TMLKyza/MyHeavyNC/LCNC-config/qtvcp/screens/qtdragon/images/brushed_metal.png

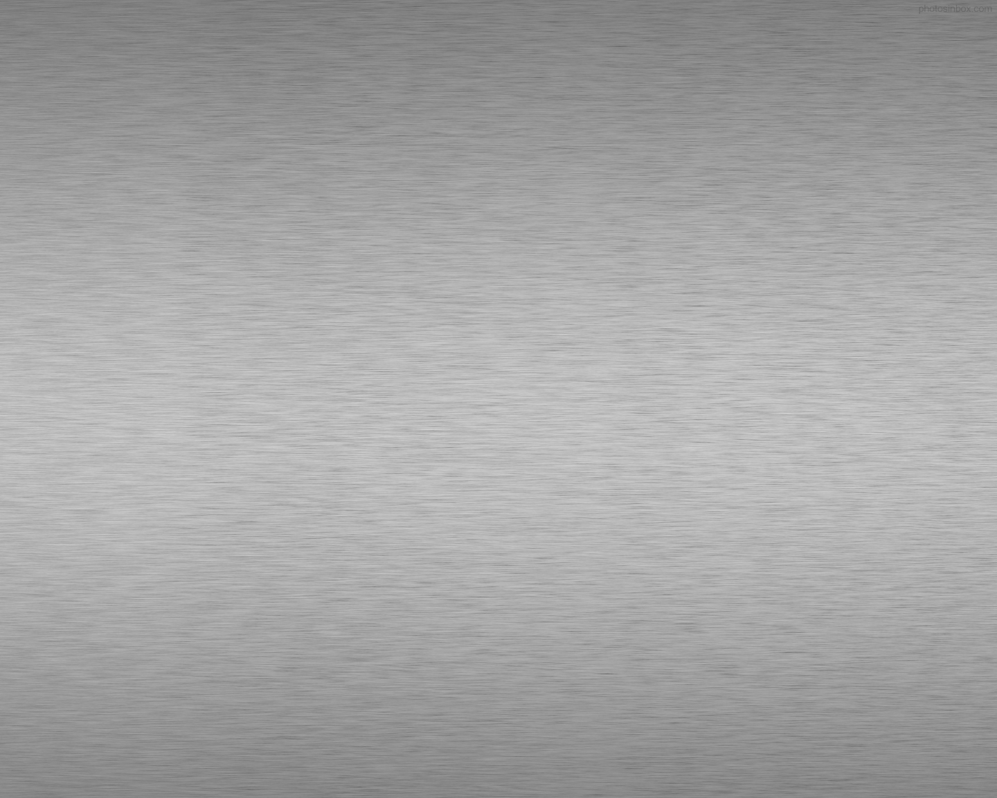
LCNC-config/qtvcp/screens/qtdragon/images/brushed_metal.png
