TMLKyza/MyHeavyNC/LCNC-config/qtvcp/screens/qtdragon/images/atc_spindle_tool.png

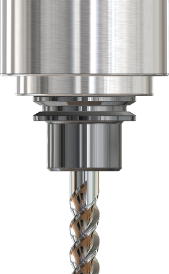
LCNC-config/qtvcp/screens/qtdragon/images/atc_spindle_tool.png
