TMLKyza/MyHeavyNC/LCNC-config/qtvcp/screens/qtdragon/images/Left_arrow.png

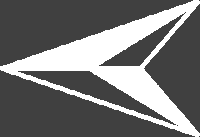
LCNC-config/qtvcp/screens/qtdragon/images/Left_arrow.png
