TMLKyza/MyHeavyNC/LCNC-config/qtvcp/screens/qtdragon/images/Right_arrow.png

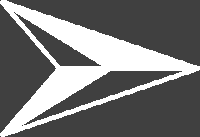
LCNC-config/qtvcp/screens/qtdragon/images/Right_arrow.png
