TMLKyza/MyHeavyNC/LCNC-config/qtvcp/screens/qtdragon/images/tool_probe.png

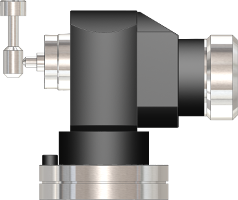
LCNC-config/qtvcp/screens/qtdragon/images/tool_probe.png
