TMLKyza/MyHeavyNC/LCNC-config/qtvcp/screens/qtdragon/images/x_minus_jog_button.png

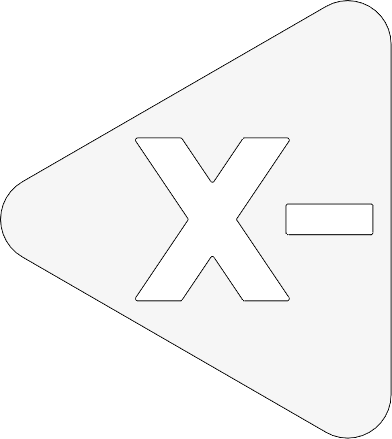
LCNC-config/qtvcp/screens/qtdragon/images/x_minus_jog_button.png
