TMLKyza/MyHeavyNC/LCNC-config/qtvcp/screens/qtdragon/images/x_plus_jog_button.png

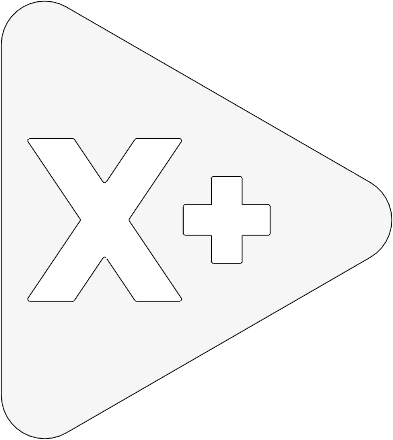
LCNC-config/qtvcp/screens/qtdragon/images/x_plus_jog_button.png
