TMLKyza/MyHeavyNC/LCNC-config/qtvcp/screens/qtdragon/images/y_plus_jog_button.png

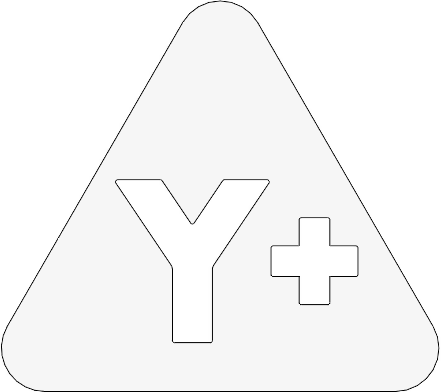
LCNC-config/qtvcp/screens/qtdragon/images/y_plus_jog_button.png
