TMLKyza/MyHeavyNC/LCNC-config/qtvcp/screens/qtdragon/images/z_minus_jog_button.png

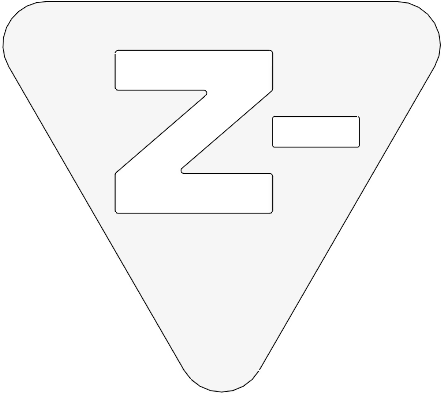
LCNC-config/qtvcp/screens/qtdragon/images/z_minus_jog_button.png
