TMLKyza/MyHeavyNC/CAD/Users/CAD/Documents/SOLIDWORKS/Router/parts/Yaxis/YstepperMount.step

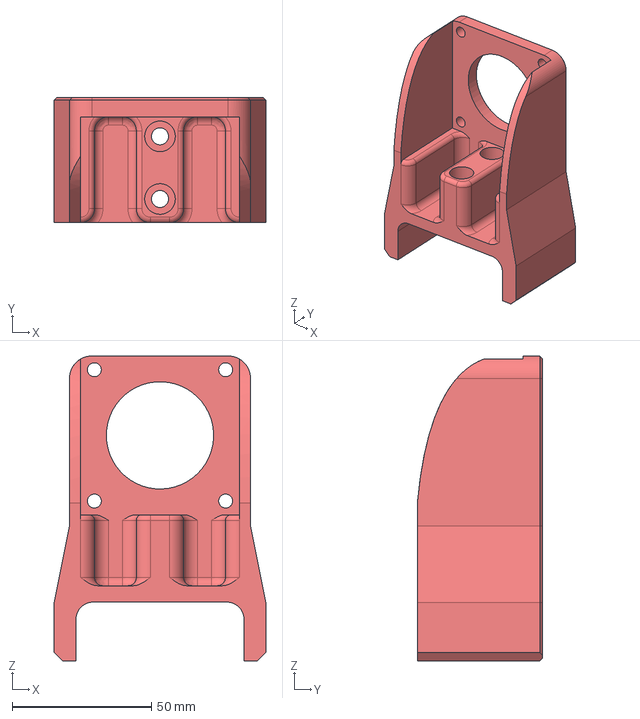
[picture p26: CAD file, 2024-07-04]
CAD/Users/CAD/Documents/SOLIDWORKS/Router/parts/Yaxis/YstepperMount.step
76.0 x 45.0 x 109.5 mm
