TMLKyza/MyHeavyNC/CAD/Users/CAD/Documents/SOLIDWORKS/Router/parts/Zaxis/motorSupport.SLDPRT

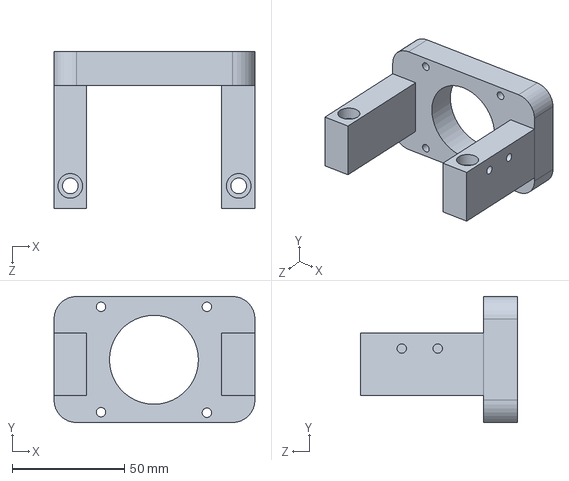
[picture p27: CAD file, 2024-07-04]
CAD/Users/CAD/Documents/SOLIDWORKS/Router/parts/Zaxis/motorSupport.SLDPRT
89.5 x 56.2 x 69.8 mm
