TMLKyza/MyHeavyNC/CAD/Users/CAD/Documents/SOLIDWORKS/vice/jaws.SLDPRT

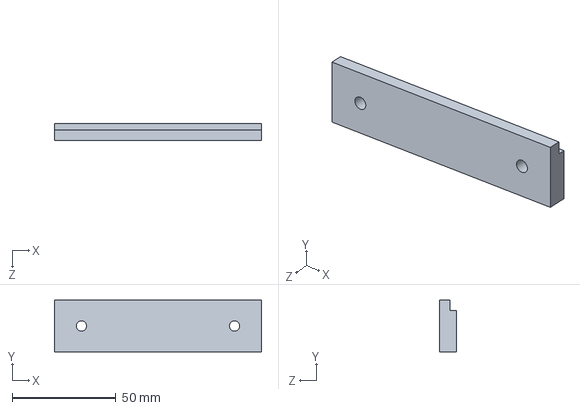
[picture p28: CAD file, 2024-07-04]
CAD/Users/CAD/Documents/SOLIDWORKS/vice/jaws.SLDPRT
100.0 x 25.0 x 8.00 mm
