TMLKyza/MyHeavyNC/CAD/parts/HRG25Rail.SLDPRT

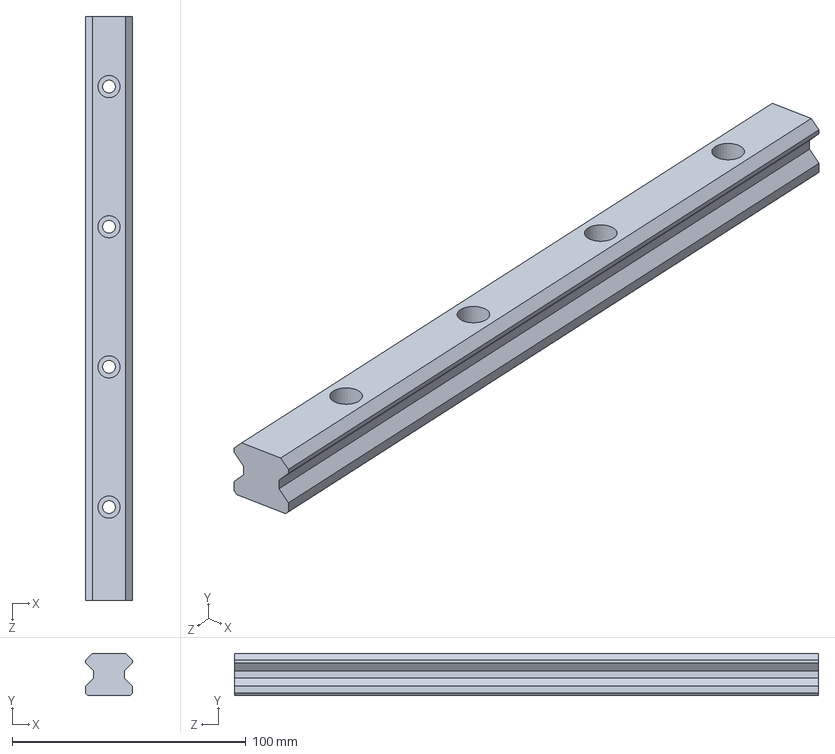
[picture p29: CAD file, 2024-07-04]
CAD/parts/HRG25Rail.SLDPRT
20.0 x 18.0 x 250.0 mm
