TMLKyza/MyHeavyNC/CAD/parts/Xaxis/support BF12.step

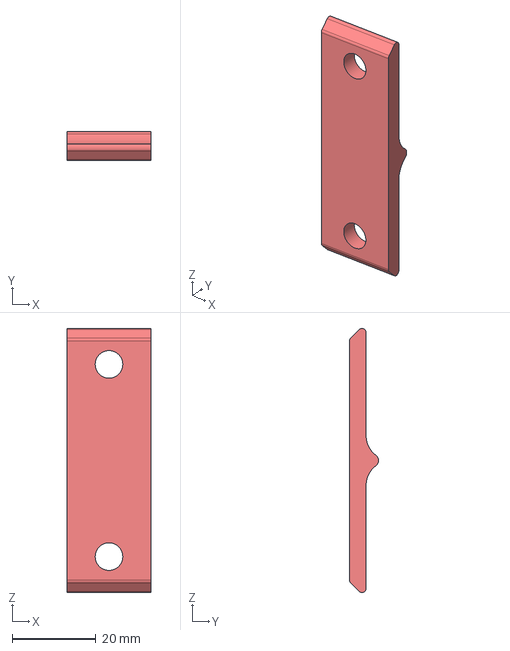
[picture p30: CAD file, 2024-07-04]
CAD/parts/Xaxis/support BF12.step
20.0 x 7.00 x 63.2 mm
