TMLKyza/MyHeavyNC/CAD/parts/Yaxis/Yaxis_tube.SLDPRT

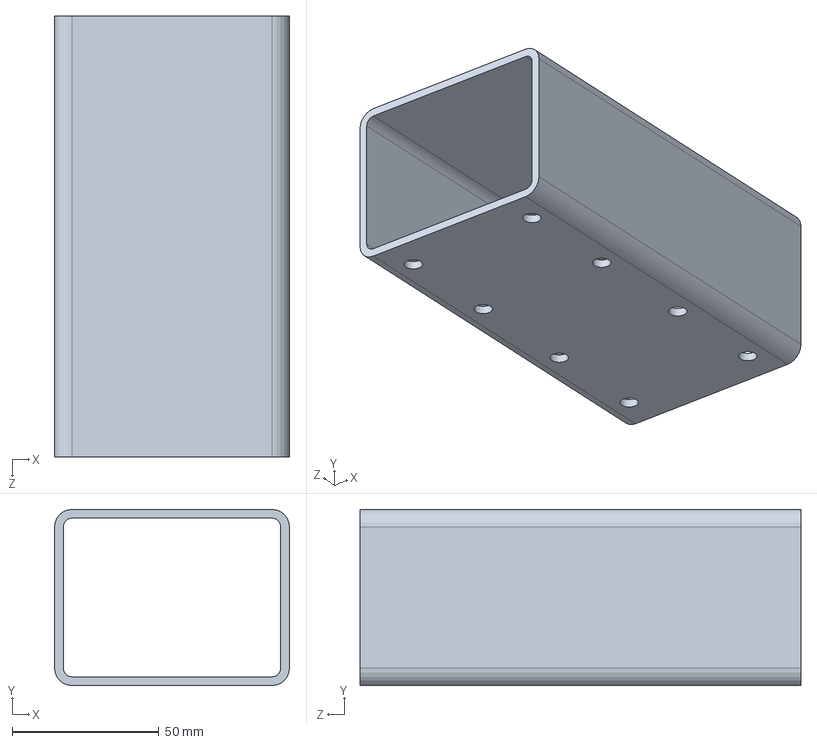
[picture p31: CAD file, 2024-07-04]
CAD/parts/Yaxis/Yaxis_tube.SLDPRT
80.0 x 60.0 x 150.0 mm
