TMLKyza/MyHeavyNC/CAD/Users/CAD/Documents/SOLIDWORKS/Router/parts/Xaxis/XsensorSupport.SLDPRT

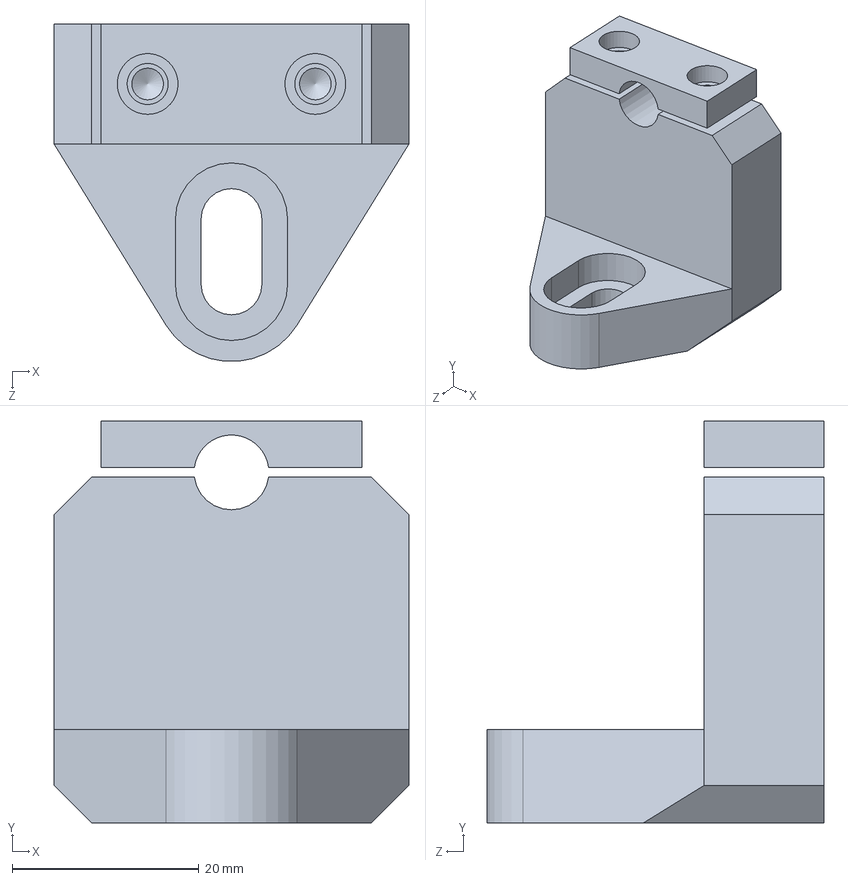
[picture p32: CAD file, 2024-07-04]
CAD/Users/CAD/Documents/SOLIDWORKS/Router/parts/Xaxis/XsensorSupport.SLDPRT
37.9 x 43.0 x 36.1 mm
