TMLKyza/MyHeavyNC/CAD/Users/CAD/Documents/SOLIDWORKS/Router/parts/Zaxis/SFU1204-nutCasing.SLDPRT

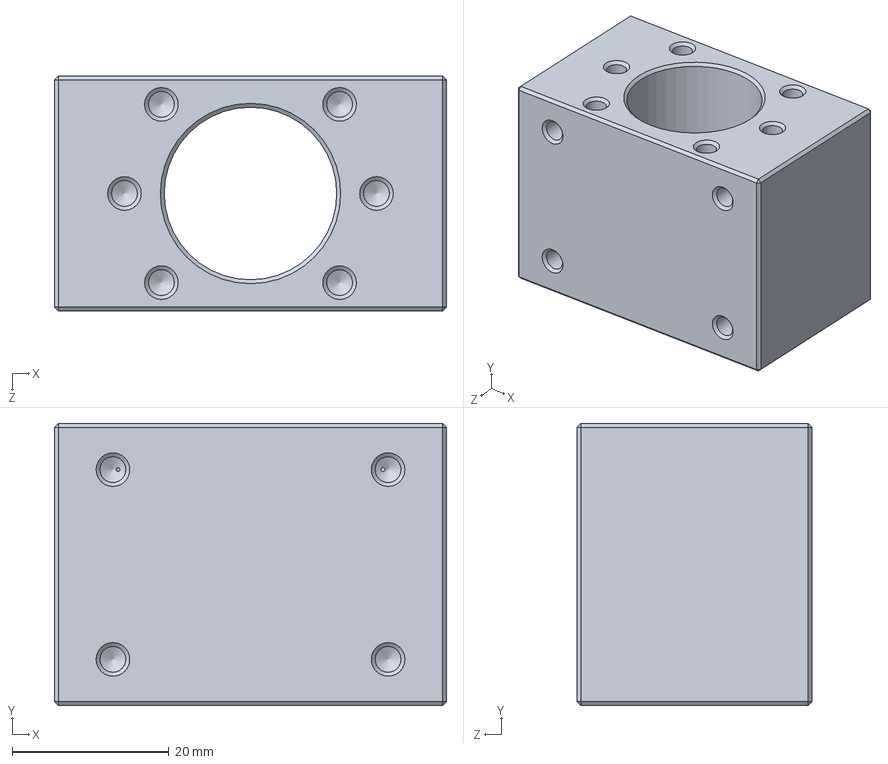
[picture p33: CAD file, 2024-07-04]
CAD/Users/CAD/Documents/SOLIDWORKS/Router/parts/Zaxis/SFU1204-nutCasing.SLDPRT
50.0 x 36.0 x 30.0 mm
