TMLKyza/MyHeavyNC/CAD/parts/Base/hole_caps.SLDPRT

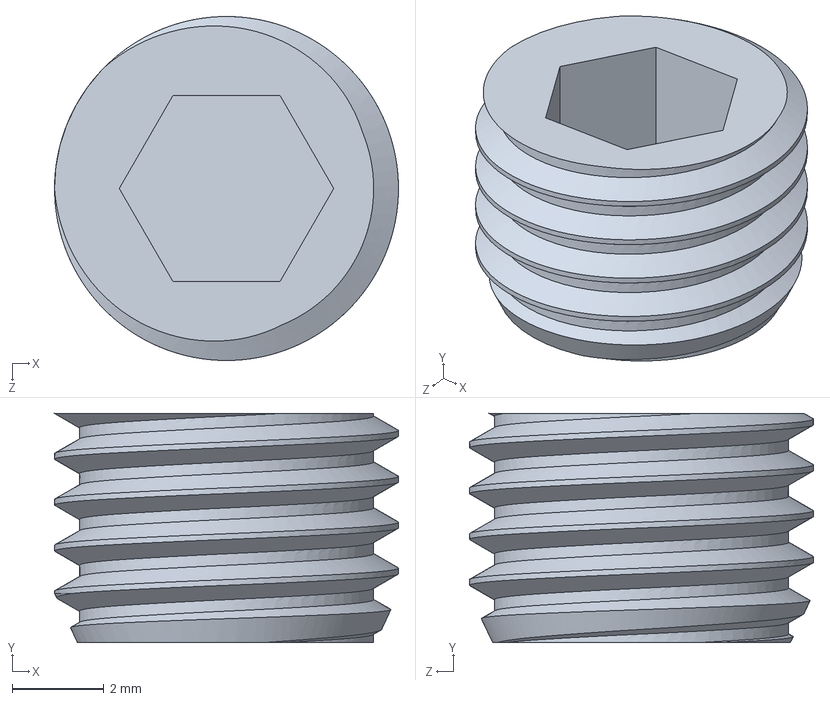
[picture p34: CAD file, 2024-07-04]
CAD/parts/Base/hole_caps.SLDPRT
7.50 x 5.00 x 7.50 mm
