TMLKyza/MyHeavyNC/CAD/parts/BK12.step

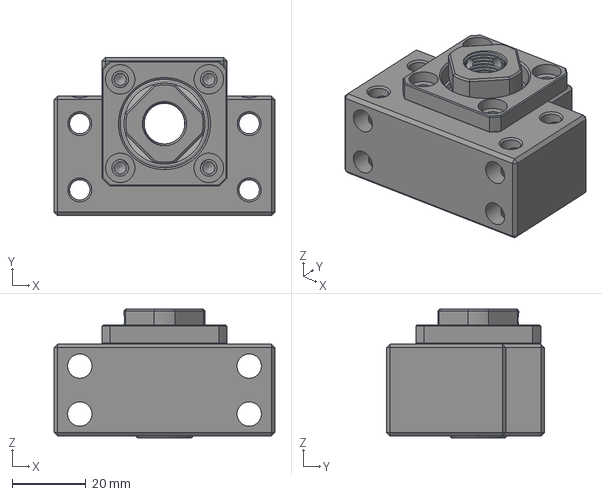
[picture p35: CAD file, 2024-07-04]
CAD/parts/BK12.step
60.0 x 43.0 x 35.0 mm
