TMLKyza/MyHeavyNC/CAD/parts/Xaxis/Lsupport.step

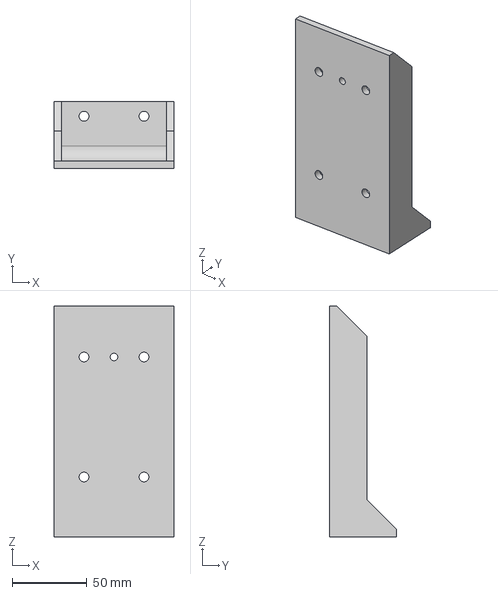
[picture p36: CAD file, 2024-07-04]
CAD/parts/Xaxis/Lsupport.step
80.0 x 45.0 x 154.0 mm
