TMLKyza/MyHeavyNC/CAD/parts/Yaxis/BK12 Blocksupport.step

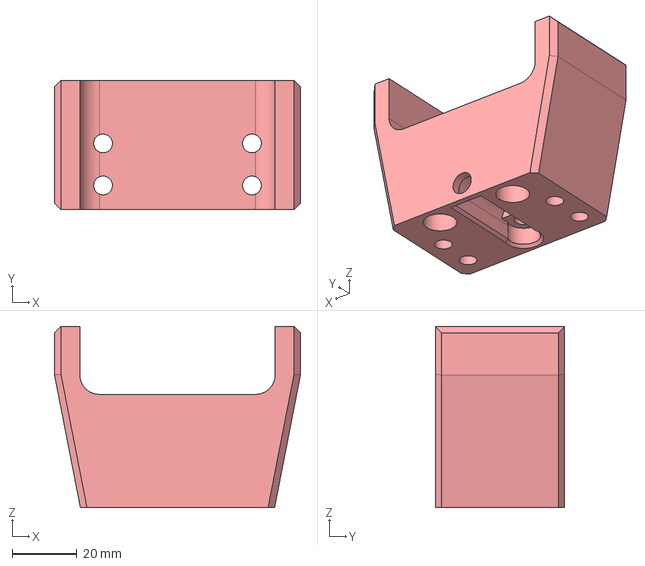
[picture p37: CAD file, 2024-07-04]
CAD/parts/Yaxis/BK12 Blocksupport.step
76.0 x 40.0 x 56.0 mm
