TMLKyza/MyHeavyNC/CAD/Users/CAD/Documents/SOLIDWORKS/Router/parts/Zaxis/XcarriageSpacer.SLDPRT

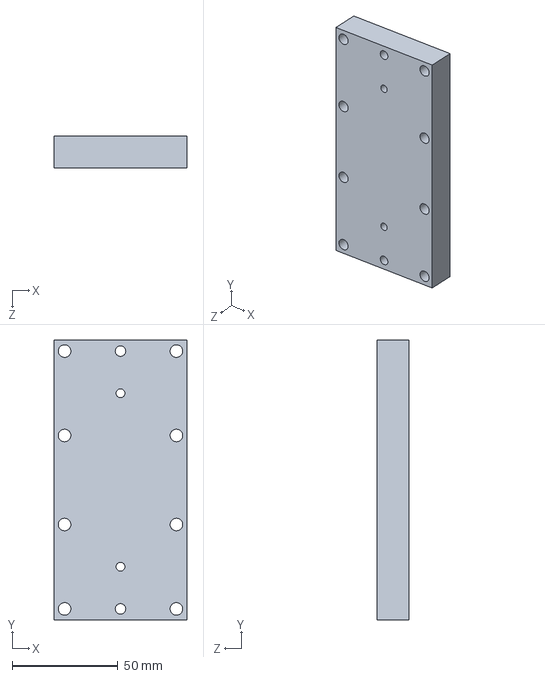
[picture p38: CAD file, 2024-07-04]
CAD/Users/CAD/Documents/SOLIDWORKS/Router/parts/Zaxis/XcarriageSpacer.SLDPRT
63.0 x 132.7 x 15.0 mm
