TMLKyza/MyHeavyNC/CAD/parts/Base/epoxygraniteCast.SLDPRT

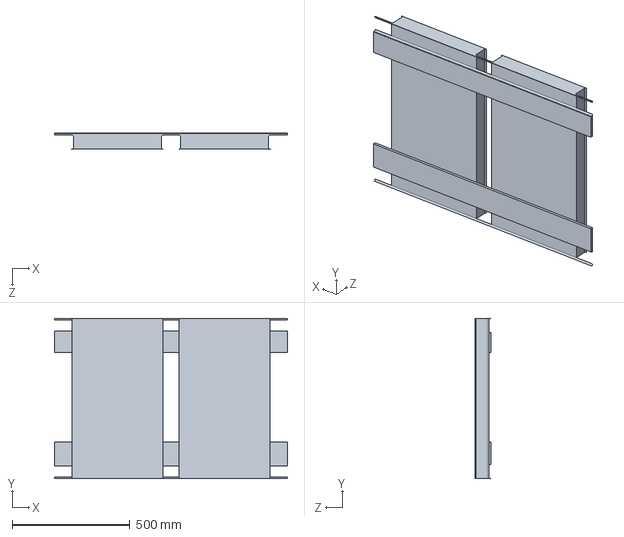
[picture p39: CAD file, 2024-07-04]
CAD/parts/Base/epoxygraniteCast.SLDPRT
990.0 x 680.0 x 70.0 mm
