TMLKyza/MyHeavyNC/CAD/parts/SFU.SLDPRT

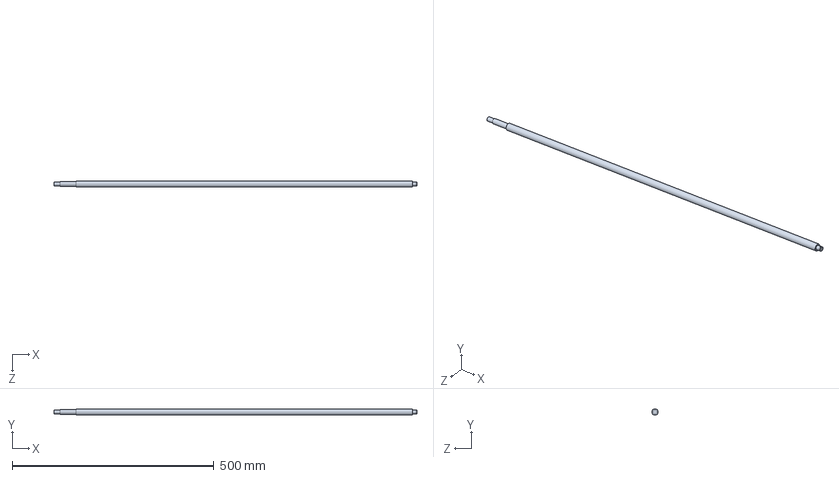
[picture p40: CAD file, 2024-07-04]
CAD/parts/SFU.SLDPRT
900.0 x 16.0 x 16.0 mm
