TMLKyza/MyHeavyNC/CAD/parts/Yaxis/BF12 Block.step

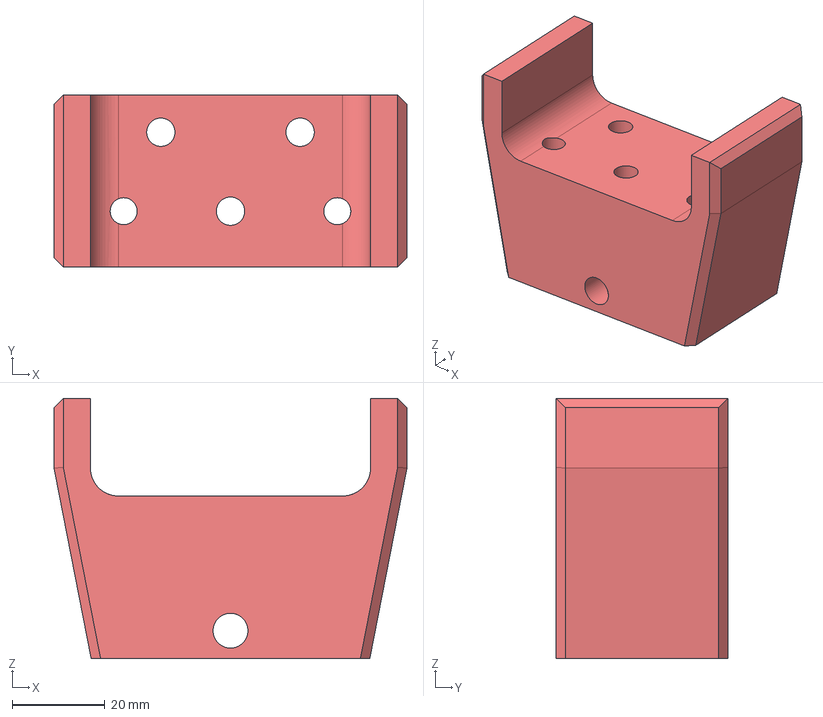
[picture p41: CAD file, 2024-07-04]
CAD/parts/Yaxis/BF12 Block.step
76.0 x 37.0 x 56.0 mm
