TMLKyza/MyHeavyNC/CAD/parts/Zaxis/2_2kw_spindle v2.step

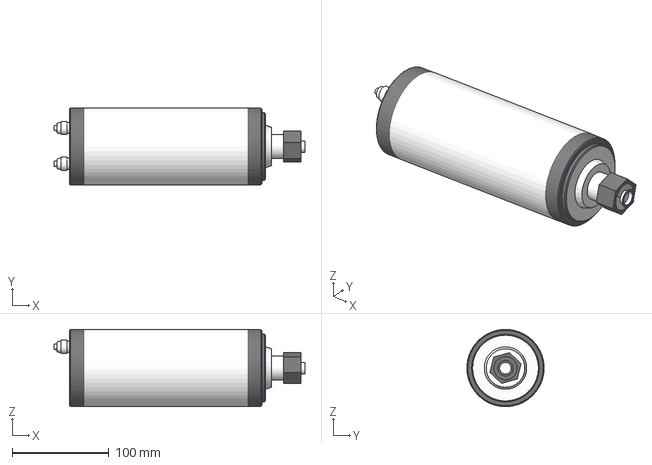
[picture p42: CAD file, 2024-07-04]
CAD/parts/Zaxis/2_2kw_spindle v2.step
259.7 x 80.0 x 79.9 mm
