TMLKyza/MyHeavyNC/CAD/parts/nema23.step

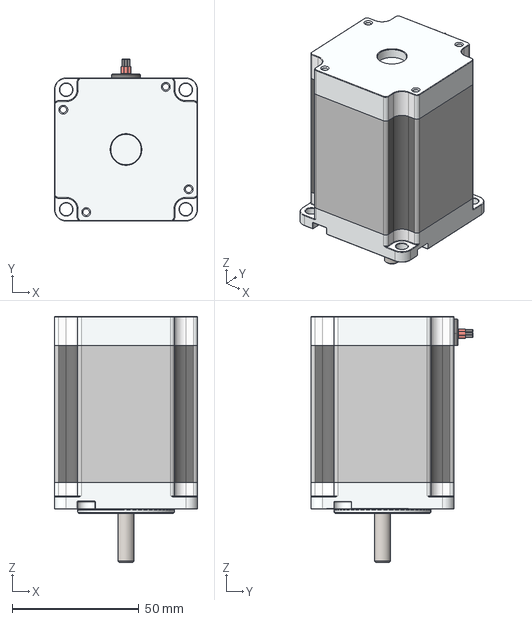
[picture p43: CAD file, 2024-07-04]
CAD/parts/nema23.step
56.4 x 63.9 x 97.0 mm
