TMLKyza/MyHeavyNC/CAD/parts/Xaxis/support BK12.step

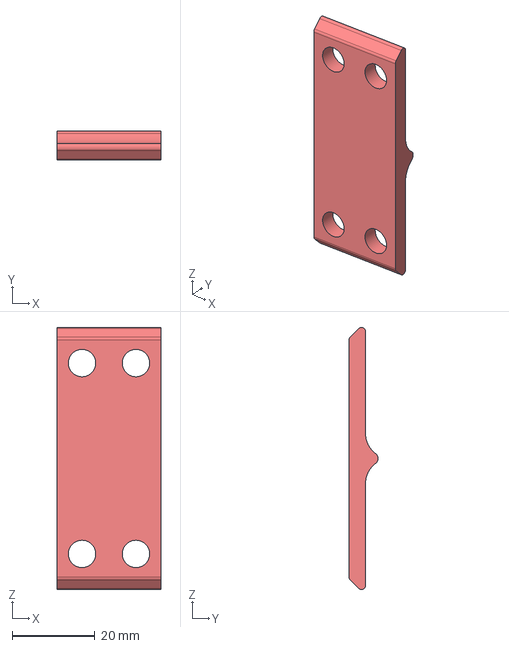
[picture p44: CAD file, 2024-07-04]
CAD/parts/Xaxis/support BK12.step
25.0 x 7.00 x 63.2 mm
