TMLKyza/MyHeavyNC/CAD/parts/BF12.step

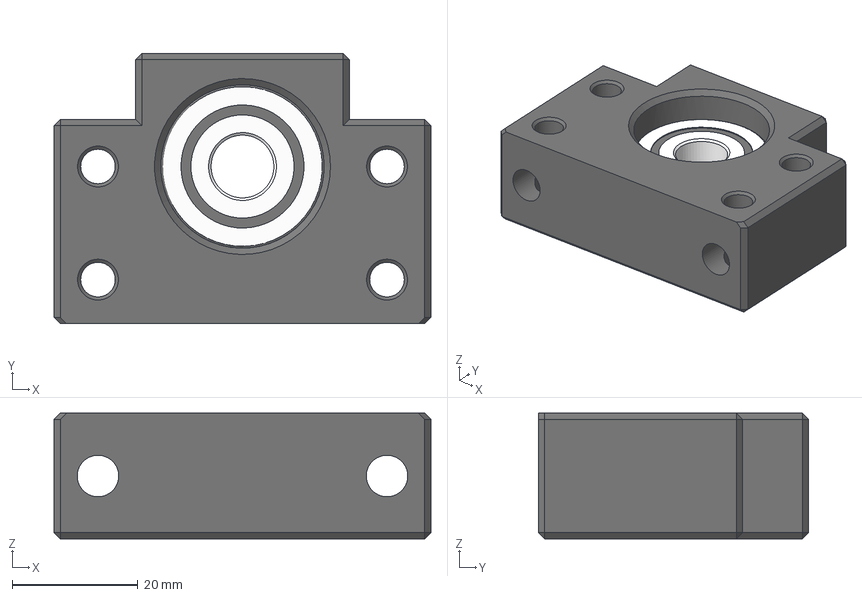
[picture p45: CAD file, 2024-07-04]
CAD/parts/BF12.step
60.0 x 43.0 x 20.0 mm
