TMLKyza/MyHeavyNC/CAD/parts/Zaxis/BK10.step

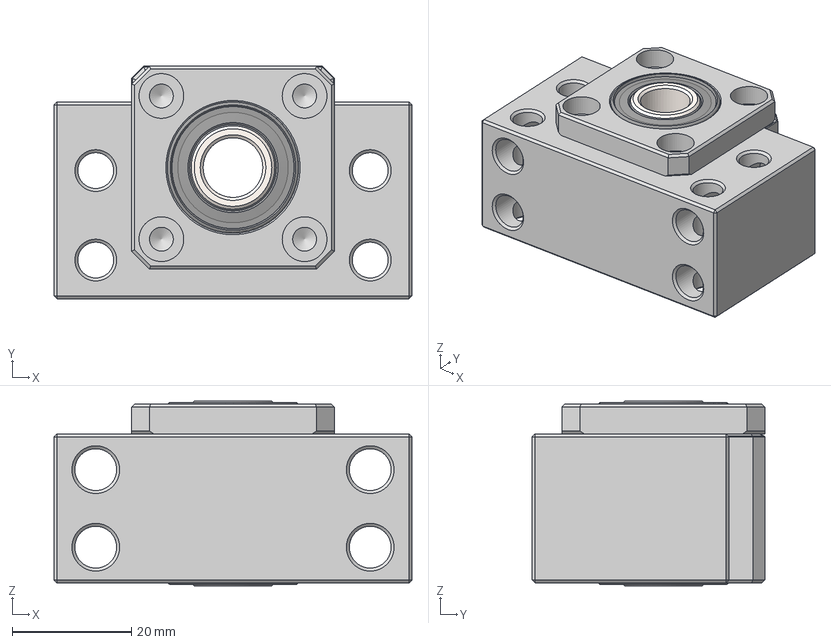
[picture p46: CAD file, 2024-07-04]
CAD/parts/Zaxis/BK10.step
60.0 x 39.0 x 31.0 mm
