TMLKyza/MyHeavyNC/CAD/Users/CAD/Documents/SOLIDWORKS/Router/parts/Zaxis/newSpindleSupport.SLDPRT

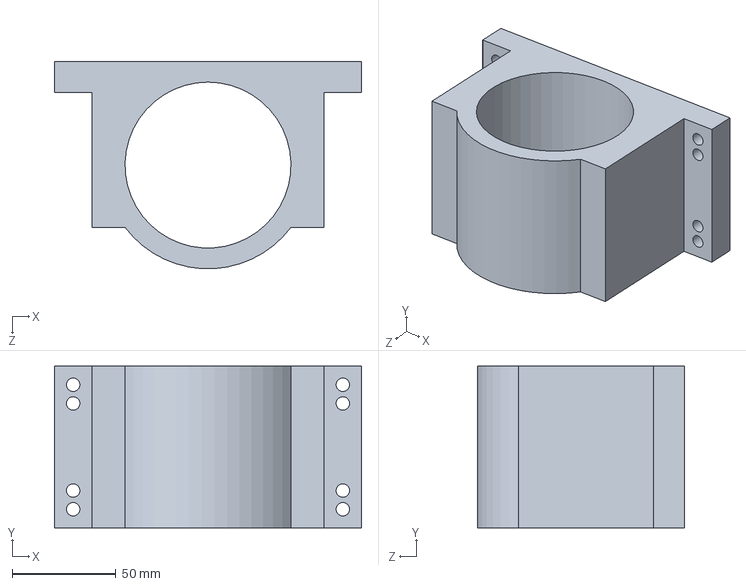
[picture p47: CAD file, 2024-07-04]
CAD/Users/CAD/Documents/SOLIDWORKS/Router/parts/Zaxis/newSpindleSupport.SLDPRT
148.0 x 78.0 x 99.9 mm
