TMLKyza/MyHeavyNC/CAD/parts/Zaxis/ZCableChainSupport.step

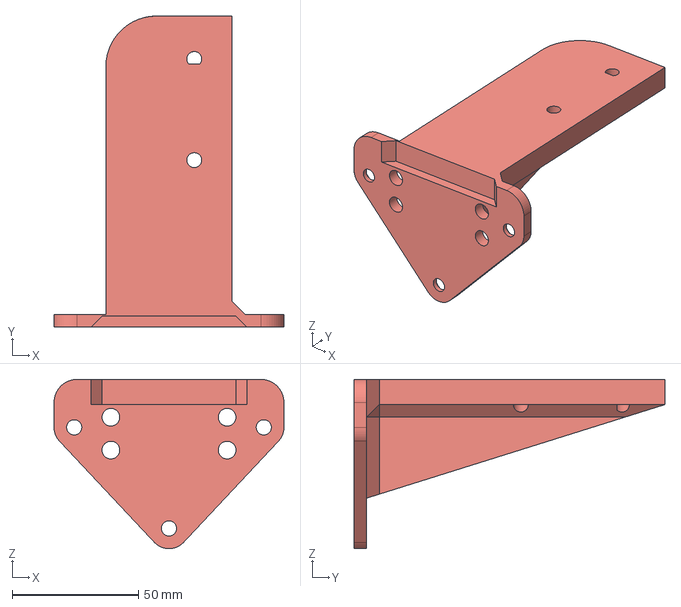
[picture p48: CAD file, 2024-07-04]
CAD/parts/Zaxis/ZCableChainSupport.step
91.0 x 123.0 x 67.0 mm
