TMLKyza/MyHeavyNC/CAD/parts/Zaxis/SFU1204-BallNut.step

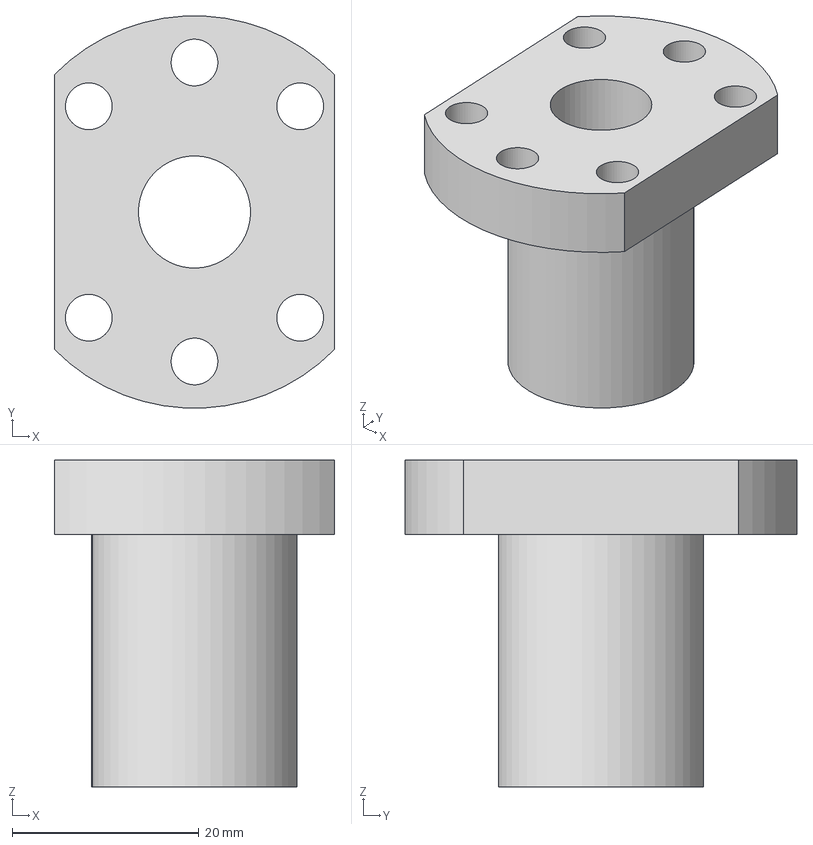
[picture p49: CAD file, 2024-07-04]
CAD/parts/Zaxis/SFU1204-BallNut.step
30.0 x 41.9 x 35.0 mm
