TMLKyza/MyHeavyNC/CAD/parts/Zaxis/BF10.STEP

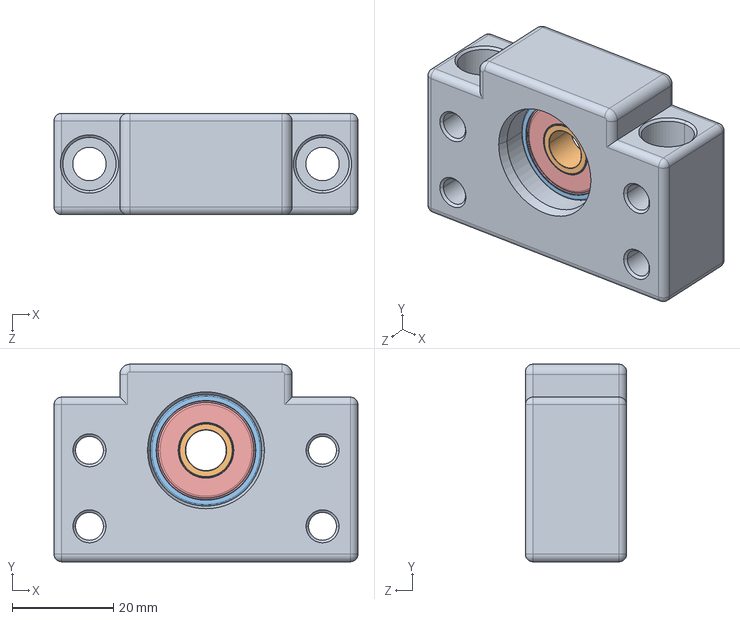
[picture p50: CAD file, 2024-07-04]
CAD/parts/Zaxis/BF10.STEP
60.0 x 39.0 x 20.0 mm
BF10軸承座_體(成_)
608ZZ軸承
