TMLKyza/MyHeavyNC/CAD/parts/Zaxis/SFU16nutHolder.step

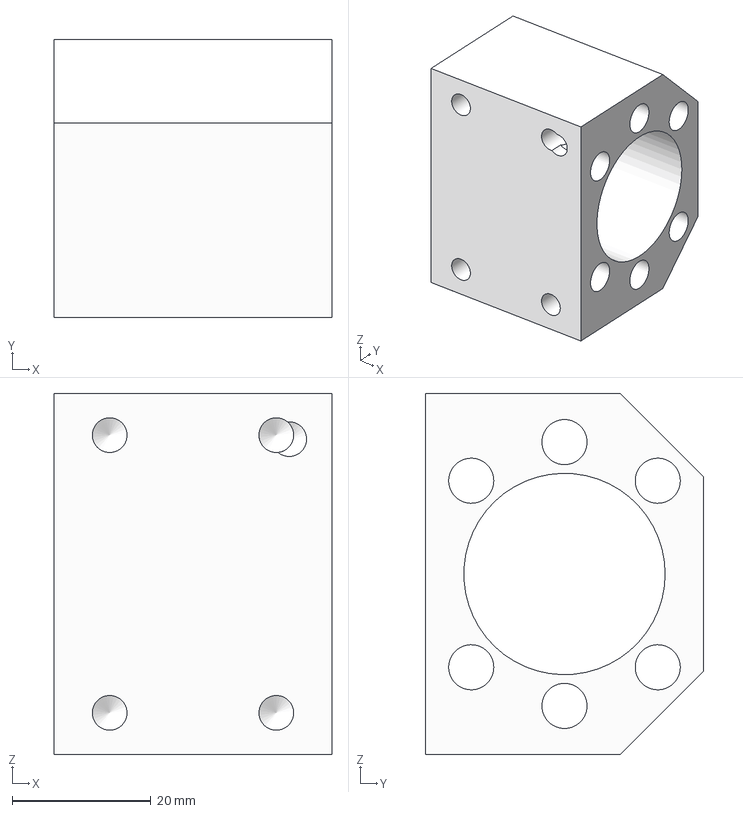
[picture p51: CAD file, 2024-07-04]
CAD/parts/Zaxis/SFU16nutHolder.step
40.0 x 40.0 x 52.0 mm
