TMLKyza/MyHeavyNC/LCNC-config/qtdragon_postgui.hal

#net spindle-speed-limited  =>  spindle.0.speed-out-rps => spindle.0.speed-in

# the unlink pin commands are only used, because they are connected 
# in core_sim.hal and we use this file to simulate
#unlinkp iocontrol.0.tool-change
#unlinkp iocontrol.0.tool-changed
#unlinkp iocontrol.0.tool-prep-number

net tool-change      hal_manualtoolchange.change   <=  iocontrol.0.tool-change 
net tool-changed     hal_manualtoolchange.changed  <=  iocontrol.0.tool-changed
net tool-prep-number hal_manualtoolchange.number   <=  iocontrol.0.tool-prep-number

# external offset spindle auto raise on pause
#net spindle-pause     qtdragon.spindle-inhibit spindle.0.inhibit
#net eoffset_clear    qtdragon.eoffset-clear => axis.z.eoffset-clear
#net eoffset_count    qtdragon.eoffset-spindle-count => axis.z.eoffset-counts
#net eoffset          qtdragon.eoffset-value <= axis.z.eoffset
#setp axis.z.eoffset-enable 1
#setp axis.z.eoffset-scale 1.0

#spindle information on display
net vfd-conection-status qtdragon.spindle-modbus-connection
net spiundle-fault qtdragon.spindle-fault
net spindle-current qtdragon.spindle-amps
net spindle-voltage qtdragon.spindle-volts
